madfam-org/ultimate-box/Examples/Mini-PowerSupply/1-powersupply-front-full.png

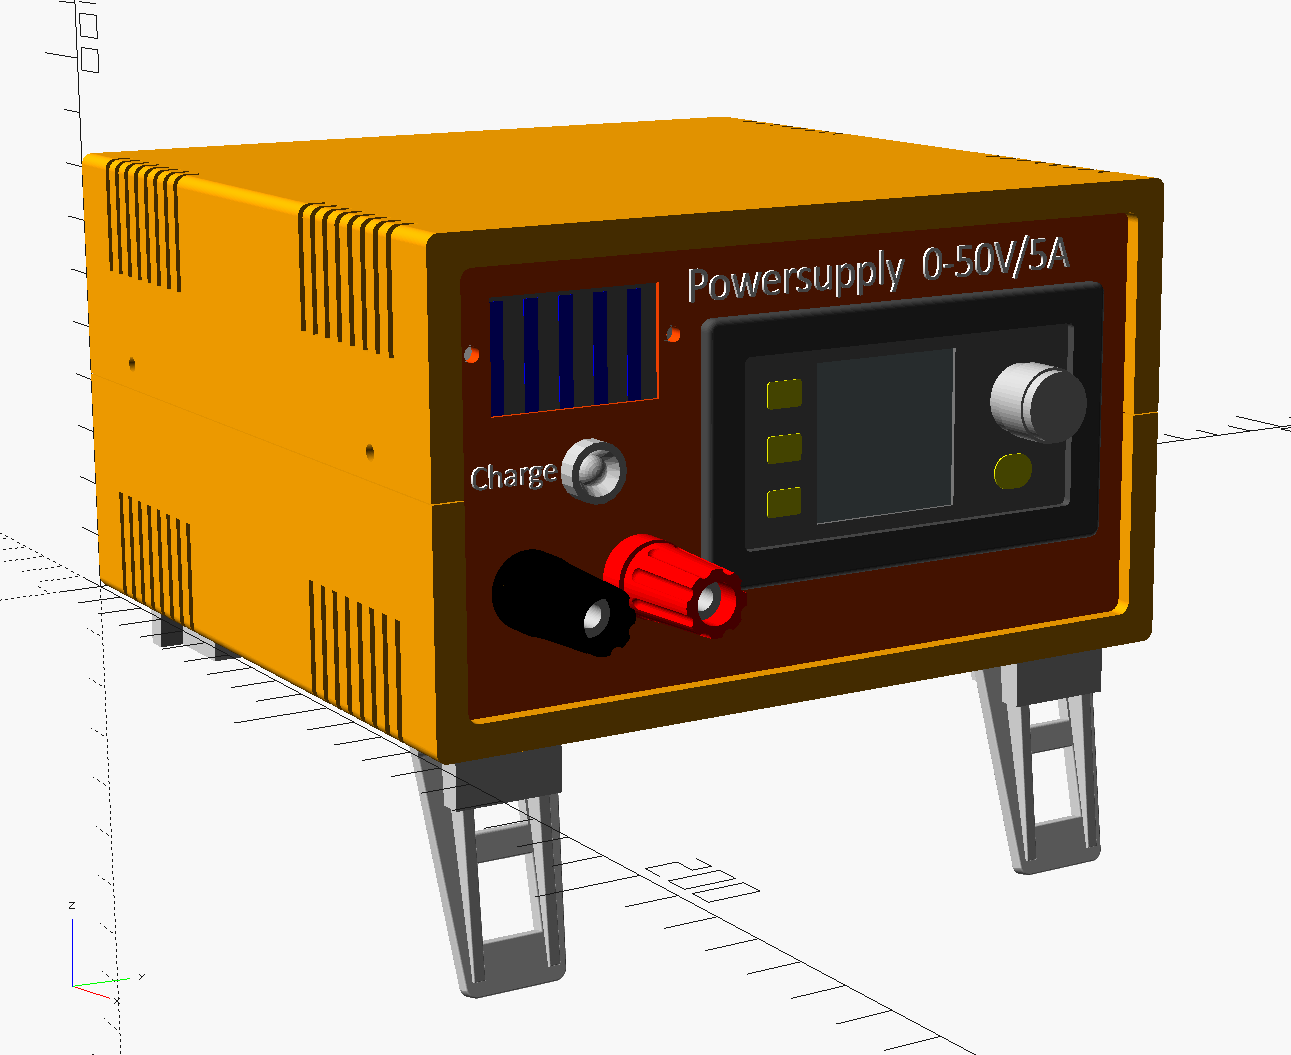
Examples/Mini-PowerSupply/1-powersupply-front-full.png
