madfam-org/ultimate-box/Examples/Mini-PowerSupply/assemblies/PowerJack.step

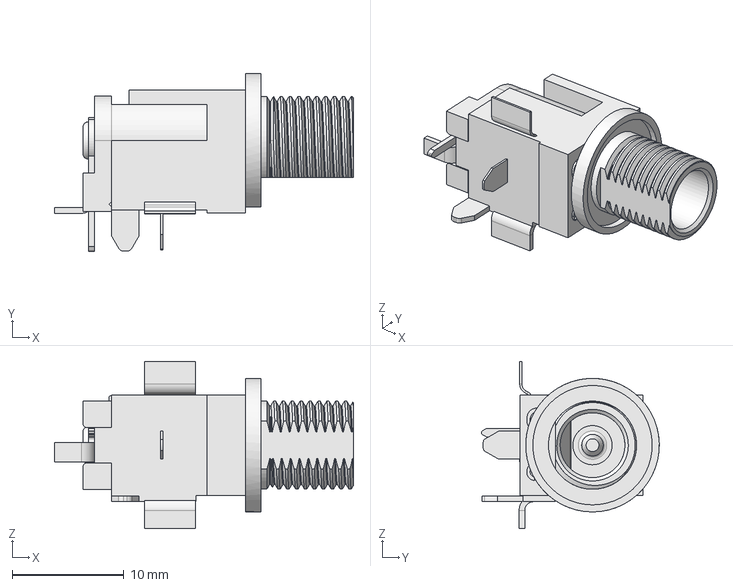
[picture p28: CAD file, 2026-02-22]
Examples/Mini-PowerSupply/assemblies/PowerJack.step
26.7 x 15.9 x 14.9 mm
