madfam-org/ultimate-box/Examples/Mini-PowerSupply/stls/Adv-Ultimate-Box-PowerSupply-Frontpanel.stl

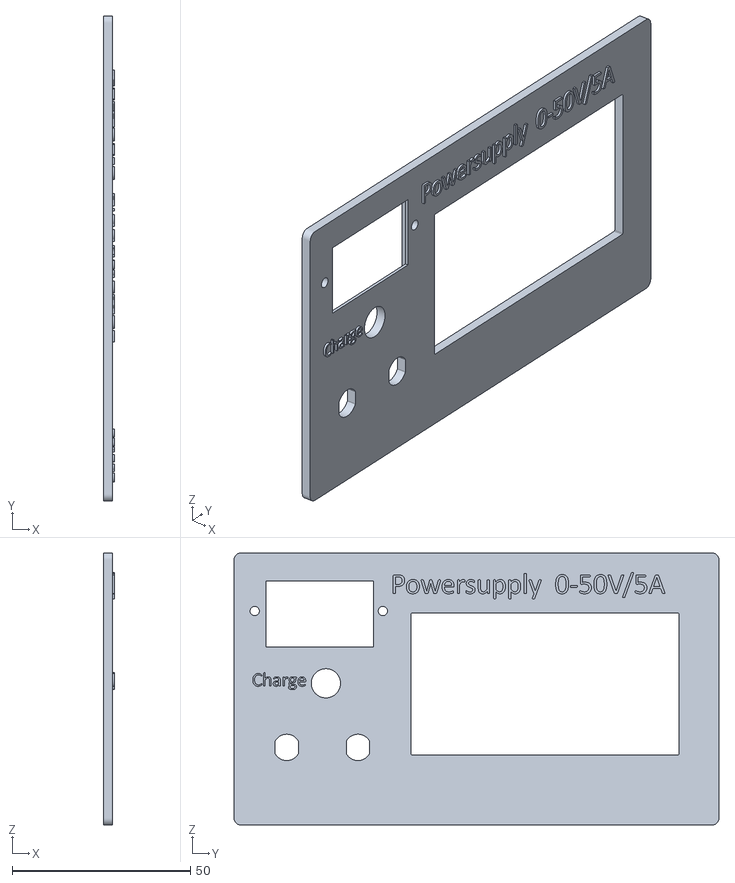
[picture p29: CAD file, 2026-02-22]
Examples/Mini-PowerSupply/stls/Adv-Ultimate-Box-PowerSupply-Frontpanel.stl
3.10 x 136.2 x 76.4
