madfam-org/ultimate-box/Examples/Mini-PowerSupply/assemblies/Relais-Holder.step

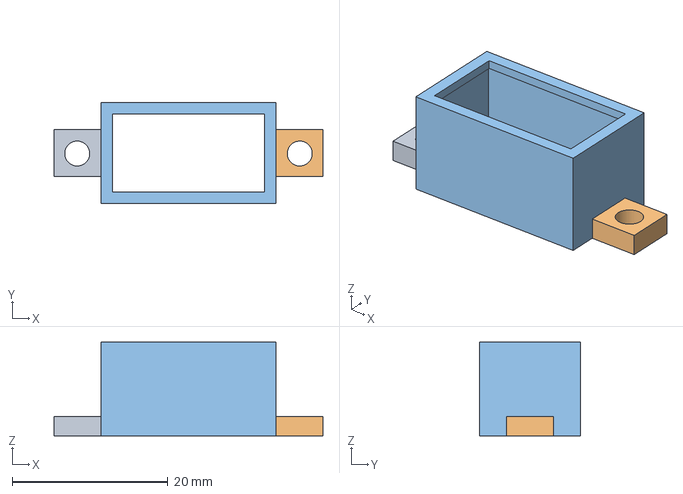
[picture p31: CAD file, 2026-02-22]
Examples/Mini-PowerSupply/assemblies/Relais-Holder.step
34.5 x 13.0 x 12.0 mm
