madfam-org/ultimate-box/Examples/Mini-PowerSupply/stls/Adv-Ultimate-Box-PowerSupply-komplett.stl

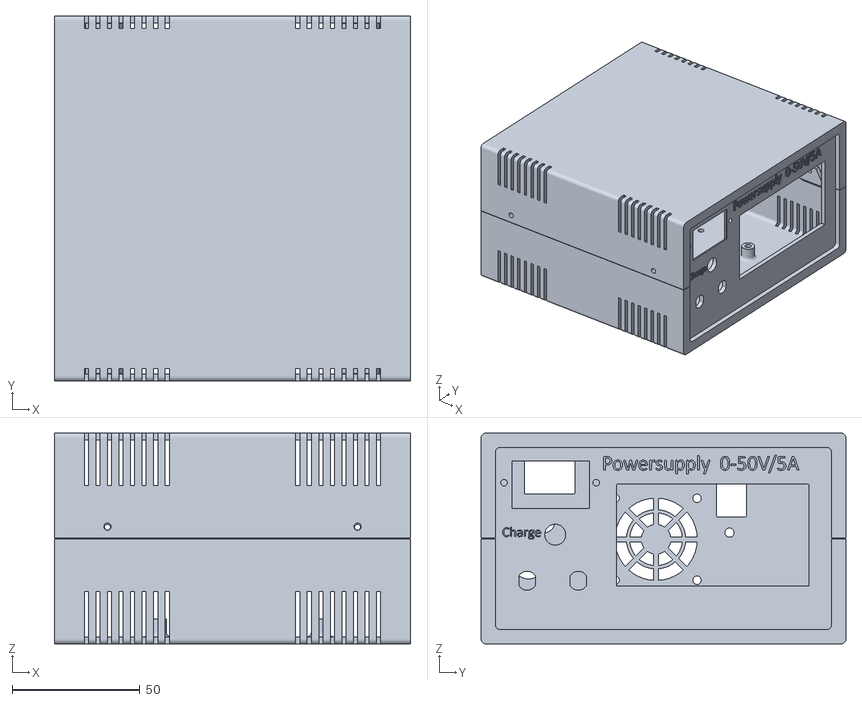
[picture p32: CAD file, 2026-02-22]
Examples/Mini-PowerSupply/stls/Adv-Ultimate-Box-PowerSupply-komplett.stl
139.2 x 142.6 x 82.4
