madfam-org/ultimate-box/Examples/Mini-PowerSupply/assemblies/LED_5mm+Socket.3mf

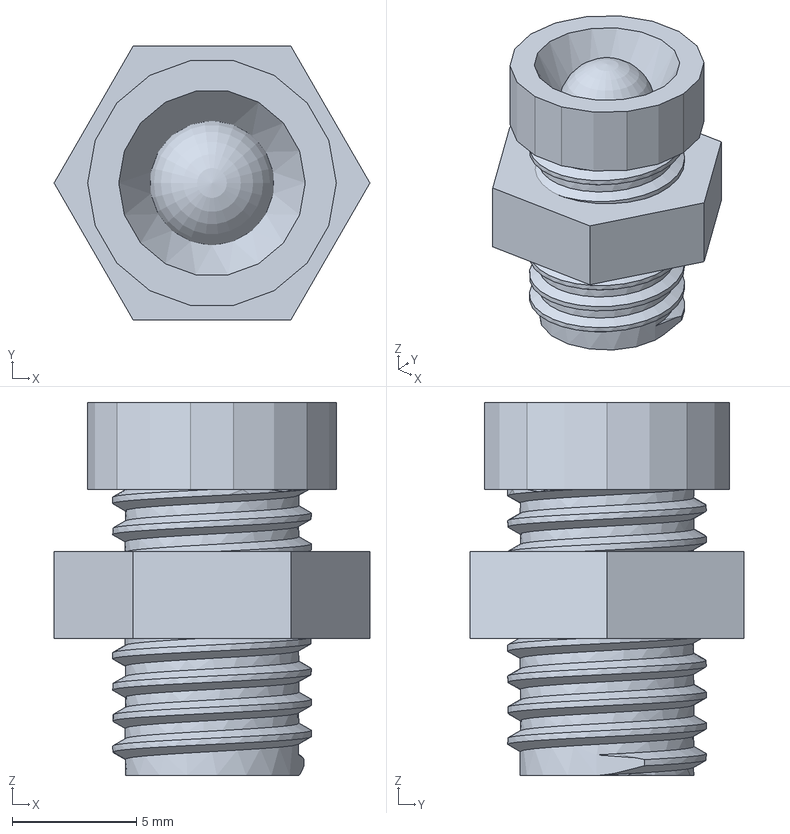
[picture p33: CAD file, 2026-02-22]
Examples/Mini-PowerSupply/assemblies/LED_5mm+Socket.3mf
12.7 x 11.0 x 15.0 mm
