madfam-org/ultimate-box/Examples/Mini-PowerSupply/assemblies/BT-Modul_BK3231.step

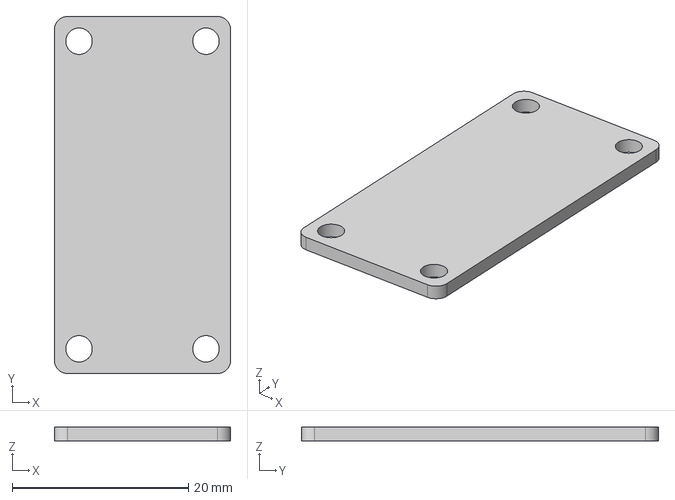
[picture p34: CAD file, 2026-02-22]
Examples/Mini-PowerSupply/assemblies/BT-Modul_BK3231.step
20.0 x 40.5 x 1.60 mm
