madfam-org/ultimate-box/Examples/Mini-PowerSupply/assemblies/PowerJackNut.step

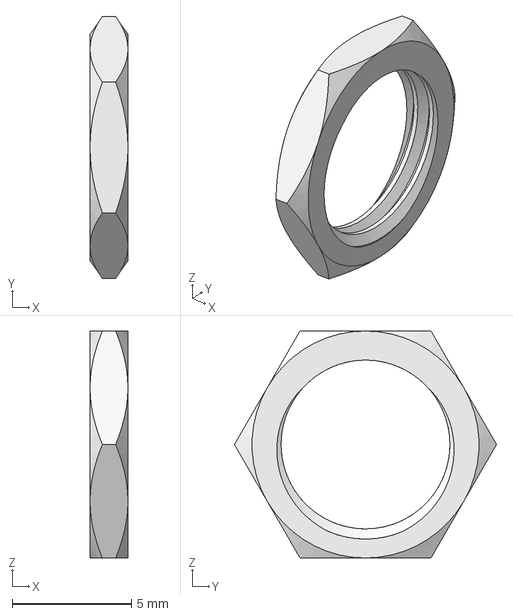
[picture p35: CAD file, 2026-02-22]
Examples/Mini-PowerSupply/assemblies/PowerJackNut.step
1.59 x 11.0 x 9.52 mm
