madfam-org/ultimate-box/Examples/Mini-PowerSupply/assemblies/AutomFuseholder.step

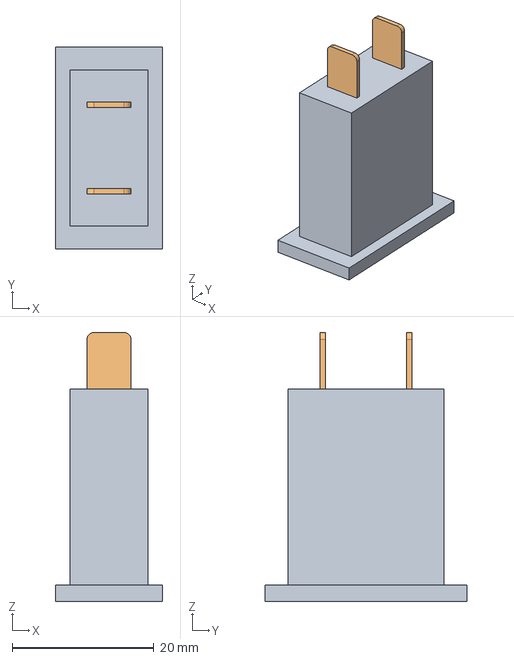
[picture p36: CAD file, 2026-02-22]
Examples/Mini-PowerSupply/assemblies/AutomFuseholder.step
15.1 x 28.5 x 38.0 mm
