madfam-org/ultimate-box/Examples/Mini-PowerSupply/assemblies/BATTERY-HOLDER_18650.stl

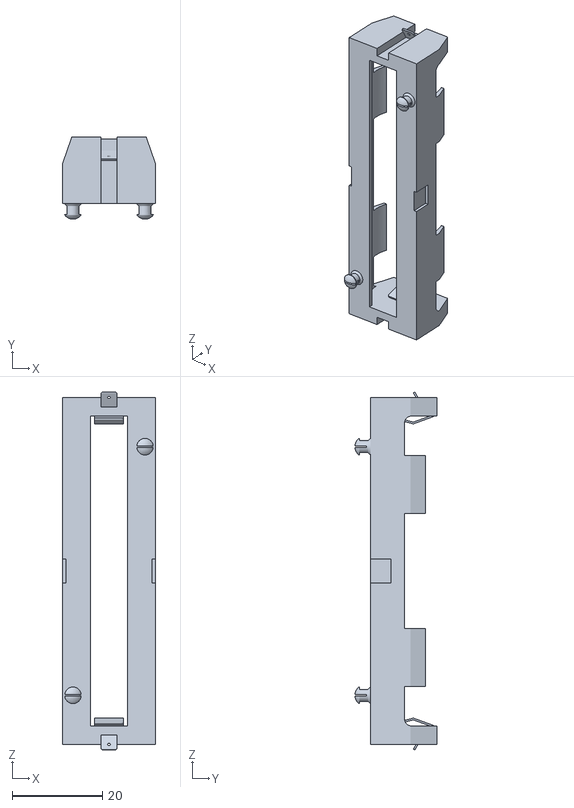
[picture p37: CAD file, 2026-02-22]
Examples/Mini-PowerSupply/assemblies/BATTERY-HOLDER_18650.stl
20.7 x 18.3 x 79.5
