madfam-org/ultimate-box/Examples/Mini-PowerSupply/assemblies/USB-Module_CH340G.step

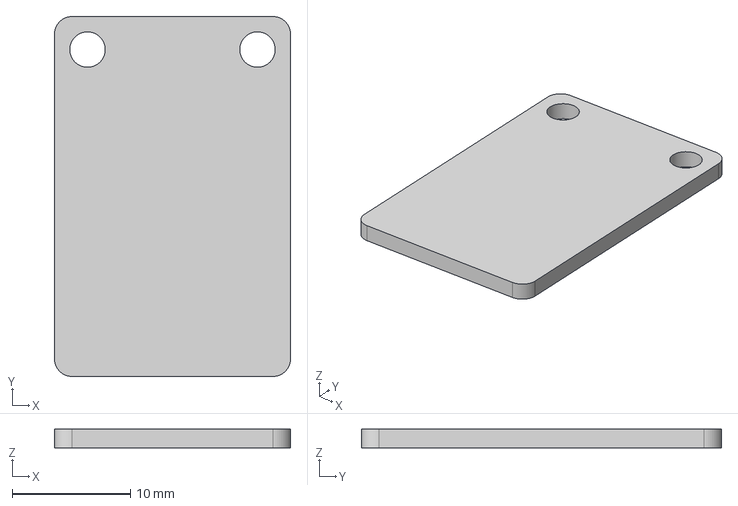
[picture p38: CAD file, 2026-02-22]
Examples/Mini-PowerSupply/assemblies/USB-Module_CH340G.step
20.0 x 30.5 x 1.60 mm
